andres-garcia-alves/electronics-dice/Resources/05-Proteus-PIC-Simulator.png

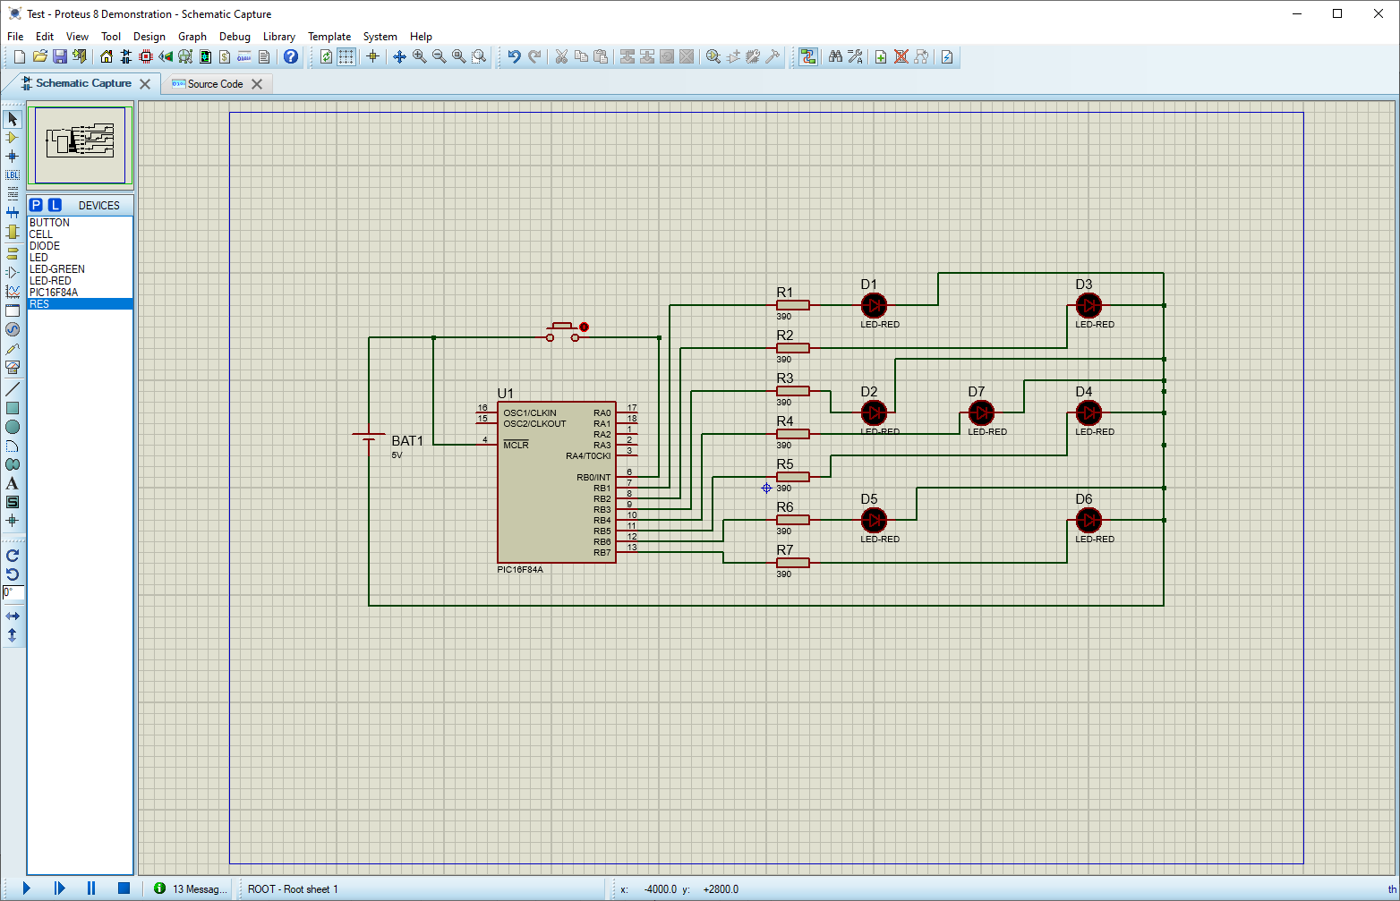
Resources/05-Proteus-PIC-Simulator.png
