andres-garcia-alves/electronics-dice/Resources/07-Building-06.jpg

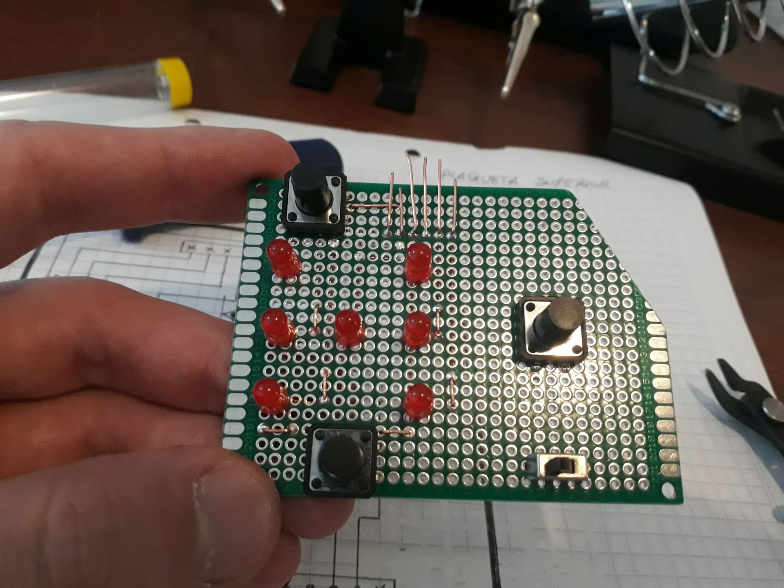
Resources/07-Building-06.jpg
